Minall13/WiFi_Radio_Project/data/branding/Internet_Radio_220.png

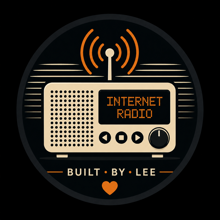
data/branding/Internet_Radio_220.png
